ale-giustina/E-ink-buddy/include/bitmaps.h

#ifndef BITMAPS_H
#define BITMAPS_H
#include <map>

// 'Clear_sky', 150x150px
const unsigned char epd_bitmap_Clear_sky [] PROGMEM = {
	0x00, 0x00, 0x00, 0x00, 0x00, 0x00, 0x00, 0x00, 0x00, 0x00, 0x00, 0x00, 0x00, 0x00, 0x00, 0x00, 
	0x00, 0x00, 0x00, 0x00, 0x00, 0x00, 0x00, 0x00, 0x00, 0x00, 0x00, 0x00, 0x00, 0x00, 0x00, 0x00, 
	0x00, 0x00, 0x00, 0x00, 0x00, 0x00, 0x00, 0x00, 0x00, 0x00, 0x00, 0x00, 0x00, 0x00, 0x00, 0x00, 
	0x00, 0x00, 0x00, 0x00, 0x00, 0x00, 0x00, 0x00, 0x00, 0x00, 0x00, 0x00, 0x00, 0x00, 0x00, 0x00, 
	0x00, 0x00, 0x00, 0x00, 0x00, 0x00, 0x00, 0x00, 0x00, 0x00, 0x00, 0x00, 0x00, 0x00, 0x00, 0x00, 
	0x00, 0x00, 0x00, 0x00, 0x00, 0x00, 0x00, 0x00, 0x00, 0x00, 0x00, 0x00, 0x00, 0x00, 0x00, 0x00, 
	0x00, 0x00, 0x00, 0x00, 0x00, 0x00, 0x00, 0x00, 0x00, 0x00, 0x00, 0x00, 0x00, 0x00, 0x00, 0x00, 
	0x00, 0x00, 0x00, 0x00, 0x00, 0x00, 0x00, 0x00, 0x00, 0x00, 0x00, 0x00, 0x00, 0x00, 0x00, 0x00, 
	0x00, 0x00, 0x00, 0x00, 0x00, 0x00, 0x00, 0x00, 0x00, 0x00, 0x00, 0x00, 0x00, 0x00, 0x00, 0x00, 
	0x00, 0x00, 0x00, 0x00, 0x00, 0x00, 0x00, 0x00, 0x00, 0x00, 0x00, 0x00, 0x00, 0x00, 0x00, 0x00, 
	0x00, 0x00, 0x00, 0x00, 0x00, 0x00, 0x00, 0x00, 0x00, 0x00, 0x00, 0x00, 0x00, 0x00, 0x00, 0x00, 
	0x00, 0x00, 0x00, 0x00, 0x00, 0x00, 0x00, 0x00, 0x00, 0x00, 0x00, 0x00, 0x00, 0x00, 0x00, 0x00, 
	0x00, 0x00, 0x00, 0x00, 0x00, 0x00, 0x00, 0x00, 0x00, 0x00, 0x00, 0x00, 0x00, 0x00, 0x00, 0x00, 
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
static const unsigned char* icons_bitmap_allArray[5] = {
	icons_bitmap_bus,
	icons_bitmap_bus,
	icons_bitmap_w_icon,
	icons_bitmap_w_graphs,
	icons_bitmap_w_graphs
};


// Array of all bitmaps for convenience. (Total bytes used to store images in PROGMEM = 51840)

static std::map<int, int> weather_codes_to_btm = {
    {0,  0},   // Clear sky
    {1,  5},   // Mainly clear
    {2,  8},   // Partly cloudy
    {3,  7},   // Overcast
    {45, 2},   // Fog
    {48, 2},   // Depositing rime fog
    {51, 4},   // Drizzle: Light intensity
    {53, 6},   // Drizzle: Moderate intensity
    {55, 1},   // Drizzle: Dense intensity
    {56, 4},   // Freezing Drizzle: Light intensity
    {57, 1},   // Freezing Drizzle: Dense intensity
    {61, 10},  // Rain: Slight intensity
    {63, 9},   // Rain: Moderate intensity
    {65, 11},  // Rain: Heavy intensity
    {66, 10},  // Freezing Rain: Light intensity
    {67, 11},  // Freezing Rain: Heavy intensity
    {71, 13},  // Snow fall: Slight intensity
    {73, 14},  // Snow fall: Moderate intensity
    {75, 17},  // Snow fall: Heavy intensity
    {77, 14},  // Snow grains
    {80, 10},  // Rain showers: Slight
    {81, 11},  // Rain showers: Moderate
    {82, 12},  // Rain showers: Violent
    {85, 13},  // Snow showers: Slight
    {86, 14},  // Snow showers: Heavy
    {95, 3},   // Thunderstorm: Slight or moderate
    {96, 12},  // Thunderstorm with slight hail
    {99, 3}   // Thunderstorm with heavy hail
};



static const int epd_bitmap_allArray_LEN = 18;
static const unsigned char* epd_bitmap_allArray[18] = {
	epd_bitmap_Clear_sky,
	epd_bitmap_Dense_drizzle,
	epd_bitmap_Fog,
	epd_bitmap_Heavy_thunder,
	epd_bitmap_Light_drizzle,
	epd_bitmap_Mainly_clear,
	epd_bitmap_Moderate_drizzle,
	epd_bitmap_Overcast,
	epd_bitmap_Partly_cloudy,
	epd_bitmap_Rain_moderate,
	epd_bitmap_Rain_slight,
	epd_bitmap_Rain_heavy,
	epd_bitmap_Slight_thunder,
	epd_bitmap_Snow_light,
	epd_bitmap_Snow_moderate,
	epd_bitmap_wi_cloud_down,
	epd_bitmap_wi_humidity,
    epd_bitmap_Snow_heavy
};
#endif // _BITMAPS_H_
