ale-giustina/E-ink-buddy/src/helpers.cpp

// Author: Alessandro Giustina
// Description: Utility helper functions and debugging tools

#include <helpers.h>

// Returns formatted part of the local time
String time_helper(char c) {
    struct tm timeinfo;
    if (getLocalTime(&timeinfo)) {
        switch (c) {
            case 'H': return timeinfo.tm_hour < 10 ? "0" + String(timeinfo.tm_hour) : String(timeinfo.tm_hour);
            case 'M': return timeinfo.tm_min < 10 ? "0" + String(timeinfo.tm_min) : String(timeinfo.tm_min);
            case 'S': return timeinfo.tm_sec < 10 ? "0" + String(timeinfo.tm_sec) : String(timeinfo.tm_sec);
            case 'd': return timeinfo.tm_mday < 10 ? "0" + String(timeinfo.tm_mday) : String(timeinfo.tm_mday);
            case 'm': return (timeinfo.tm_mon + 1) < 10 ? "0" + String(timeinfo.tm_mon + 1) : String(timeinfo.tm_mon + 1);
            case 'Y': return String(timeinfo.tm_year + 1900);
            default: return "";
        }
    }
    return "";
}

// Prints timestamp in "YYYY-MM-DD HH:MM:SS - " format
void print_timestamp() {
    String timestamp = String(time_helper('Y')) + "-" + String(time_helper('m')) + "-" + String(time_helper('d')) + " " +
                       String(time_helper('H')) + ":" + String(time_helper('M')) + ":" + String(time_helper('S')) + " - ";
    Serial.print(timestamp);
}

bool enable_debug = false;

void debug_println(const String& message, bool override_debug) {
    if (enable_debug || override_debug) {
        Serial.println(message);
    }
}
void debug_print(const String& message, bool override_debug) {
    if (enable_debug || override_debug) {
        Serial.print(message);
    }
}

void debug_print_routes(const RouteInfo* routes, int count, bool override_debug) {
    if (enable_debug || override_debug) {
        for(int i = 0; i < count; i++) {
            print_timestamp();
            Serial.print("Route: ");
            Serial.print(routes[i].shortName);
            Serial.print(", ");
            Serial.print(routes[i].longName);
            Serial.print(", Delay: ");
            Serial.print(routes[i].delay);
            Serial.print(" min, ETA: ");
            Serial.println(routes[i].eta);
        }
    }
}

void debug_print_weather_5d(const Weather_5D& weather, bool override_debug) {
    if (enable_debug || override_debug) {
        print_timestamp();
        Serial.println("5-Day Weather Forecast:");
        for (int i = 0; i < 5; i++) {
            Serial.print("Day ");
            Serial.print(i + 1);
            Serial.print(": Code=");
            Serial.print(weather.codes[i]);
            Serial.print(", Temp Min=");
            Serial.print(weather.temp_min[i]);
            Serial.print(", Temp Max=");
            Serial.print(weather.temp_max[i]);
            Serial.print(", Precipitation Probability=");
            Serial.println(weather.precipitation[i]);
        }
    }
}

void debug_print_weather_24h(const Weather_24H& weather, bool override_debug) {
    if (enable_debug || override_debug) {
        print_timestamp();
        Serial.println("24-Hour Weather Forecast:");
        Serial.print("Code=");
        Serial.print(weather.code);
        Serial.print(", Temp Min=");
        Serial.print(weather.temp_min);
        Serial.print(", Temp Max=");
        Serial.println(weather.temp_max);
        Serial.println("Hourly Precipitation Probability:");
        for (int i = 0; i < 24; i++) {
            Serial.print(weather.precipitation[i]);
            Serial.print("% - ");
        }
        Serial.println();
        Serial.println("Hourly Temperature:");
        for (int i = 0; i < 24; i++) {
            Serial.print(weather.temperature[i]);
            Serial.print("C° - ");
        }
        Serial.println();
    }
}

void debug_print_weather_now(const Weather_now& weather, bool override_debug) {
    if (enable_debug || override_debug) {
        print_timestamp();
        Serial.println("Current Weather:");
        Serial.print("Code=");
        Serial.print(weather.code);
        Serial.print(", Temp=");
        Serial.print(weather.temp);
        Serial.print(", Windspeed=");
        Serial.print(weather.windspeed);
        Serial.print(", Precipitation Probability=");
        Serial.print(weather.precipitation_probability);
        Serial.print(", Humidity=");
        Serial.println(weather.humidity);
    }
}

bool is_connected() {

    // I found WL_CONNECTED to not be reliable enough on its own so this
    // makes a lightweight HTTP request to confirm connectivity
    // This is run every minute

    if (WiFi.status() != WL_CONNECTED) return false;

    HTTPClient http;
    http.begin("http://clients3.google.com/generate_204"); // lightweight test
    int httpCode = http.GET();
    http.end();

    return (httpCode == 204);
}

bool is_DST(int year, int month, int day, int hour) {

    // The oraArrivoAFermataSelezionata provides the time in a wierd way
    // only time will tell if this is the correct solution

    // DST: from last Sunday in March 2:00 → last Sunday in October 3:00
    if (month < 3 || month > 10) return false;
    if (month > 3 && month < 10) return true;

    int lastSunday;
    if (month == 3) {
    // Find last Sunday in March
    lastSunday = 31 - ((5 * year / 4 + 4) % 7);
    return (day > lastSunday || (day == lastSunday && hour >= 2));
    } else if (month == 10) {
    // Find last Sunday in October
    lastSunday = 31 - ((5 * year / 4 + 1) % 7);
    return !(day > lastSunday || (day == lastSunday && hour >= 3));
    }
    return false;
}

int calc_delta_time(const String& eta_str) {

    struct tm now;
    getLocalTime(&now);

    int now_total_minutes = now.tm_hour * 60 + now.tm_min;

    int eta_hour = 0;
    int eta_minute = 0;

    sscanf(eta_str.c_str(), "%d:%d", &eta_hour, &eta_minute);

    int eta_total_minutes = eta_hour * 60 + eta_minute;

    int delta_minutes = eta_total_minutes - now_total_minutes;
    if (delta_minutes < -600) {
        delta_minutes += 24 * 60; // Adjust for next day only if difference is more than 10 hours negative
    }

    return delta_minutes;
}
