ale-giustina/E-ink-buddy/src/weather.cpp

// Author: Alessandro Giustina
// Description: Weather data handling implementation file

#include <weather.h>

// Map of weather codes to descriptions
std::map<int, String> weather_codes = {
    {0,  "Clear sky"},
    {1,  "Mainly clear"},
    {2,  "Partly cloudy"},
    {3,  "Overcast"},
    {45, "Fog"},
    {48, "Depositing rime fog"},
    {51, "Drizzle: Light intensity"},
    {53, "Drizzle: Moderate intensity"},
    {55, "Drizzle: Dense intensity"},
    {56, "Freezing Drizzle: Light intensity"},
    {57, "Freezing Drizzle: Dense intensity"},
    {61, "Rain: Slight intensity"},
    {63, "Rain: Moderate intensity"},
    {65, "Rain: Heavy intensity"},
    {66, "Freezing Rain: Light intensity"},
    {67, "Freezing Rain: Heavy intensity"},
    {71, "Snow fall: Slight intensity"},
    {73, "Snow fall: Moderate intensity"},
    {75, "Snow fall: Heavy intensity"},
    {77, "Snow grains"},
    {80, "Rain showers: Slight"},
    {81, "Rain showers: Moderate"},
    {82, "Rain showers: Violent"},
    {85, "Snow showers: Slight"},
    {86, "Snow showers: Heavy"},
    {95, "Thunderstorm: Slight or moderate"},
    {96, "Thunderstorm with slight hail"},
    {99, "Thunderstorm with heavy hail"}
};

String latitude = "46.0679";
String longitude = "11.1211";

void get_weather_5d(Weather_5D &w_ob, bool force_update){

    struct tm now;

    getLocalTime(&now);

    // Check if update is needed
    if(w_ob.last_update.tm_sec==-1 || w_ob.last_update.tm_min<now.tm_min-WEATHER_EXP_5D || w_ob.last_update.tm_hour!=now.tm_hour || force_update){

        debug_println("Updating...");

        HTTPClient weatherClient;

        String url = "https://api.open-meteo.com/v1/forecast?latitude=" + latitude + "&longitude=" + longitude + "&daily=weather_code,temperature_2m_max,temperature_2m_min,precipitation_probability_max&hourly=temperature_2m,precipitation_probability&models=best_match&timezone=Europe%2FBerlin&forecast_days=14";

        weatherClient.begin(url);
        int httpCode = weatherClient.GET();
        debug_println(String("Code: ")+String(httpCode));
        if (httpCode == 200) {
            
            String payload = weatherClient.getString();
            JsonDocument doc;
            
            if (!deserializeJson(doc, payload)) {
            
                JsonObject root = doc.as<JsonObject>();

                JsonObject daily = root["daily"];
                int inx = 0;

                getLocalTime(&w_ob.last_update);

                for (JsonVariant v : daily["weather_code"].as<JsonArray>()) {
                    w_ob.codes[inx++] = v.as<short>();
                    if(inx==14)break;
                }
                inx = 0;
                for (JsonVariant v : daily["temperature_2m_max"].as<JsonArray>()) {
                    w_ob.temp_max[inx++] = v.as<float>();
                    if(inx==14)break;
                }
                inx = 0;
                for (JsonVariant v : daily["temperature_2m_min"].as<JsonArray>()) {
                    w_ob.temp_min[inx++] = v.as<float>();
                    if(inx==14)break;
                }
                inx = 0;
                for (JsonVariant v : daily["precipitation_probability_max"].as<JsonArray>()) {
                    w_ob.precipitation[inx++] = v.as<short>();
                    if(inx==14)break;
                }
                inx = 0;
                JsonObject hourly = root["hourly"];
                for (JsonVariant v : hourly["temperature_2m"].as<JsonArray>()) {
                    w_ob.temperature[inx++] = v.as<float>();
                    if(inx==336)break;
                }
                inx = 0;
                for (JsonVariant v : hourly["precipitation_probability"].as<JsonArray>()) {
                    w_ob.precipitation_probability[inx++] = v.as<short>();
                    if(inx==336)break;
                }

            } else {
            Serial.println("Failed to parse 5d weather JSON");
            debug_println(payload);
            }
        } else {
            Serial.printf("Failed to fetch weather, HTTP code: %d\n", httpCode);
        }
        weatherClient.end();
    }
    else{
        debug_println(String("Using cache"));
    }

}

void get_weather_24h(Weather_24H &w_ob, bool force_update){

    struct tm now;

    getLocalTime(&now);

    // Check if update is needed
    if(w_ob.last_update.tm_sec==-1 || w_ob.last_update.tm_min<now.tm_min-WEATHER_EXP_24H || w_ob.last_update.tm_hour!=now.tm_hour || force_update){

        debug_println("Updating...");

        HTTPClient weatherClient;

        String url = "https://api.open-meteo.com/v1/forecast?latitude=" + latitude + "&longitude=" + longitude + "&daily=temperature_2m_max,temperature_2m_min,weather_code&hourly=temperature_2m,precipitation_probability,relative_humidity_2m,cloud_cover&models=best_match&timezone=Europe%2FBerlin&forecast_days=7";

        weatherClient.begin(url);
        int httpCode = weatherClient.GET();
        debug_println(String("Code: ")+String(httpCode));
        if (httpCode == 200) {
            
            String payload = weatherClient.getString();
            JsonDocument doc;
            
            if (!deserializeJson(doc, payload)) {
            
                JsonObject root = doc.as<JsonObject>();

                JsonObject daily = root["daily"];

                getLocalTime(&w_ob.last_update);

                w_ob.code = daily["weather_code"][0].as<short>();
                w_ob.temp_max = daily["temperature_2m_max"][0].as<float>();
                w_ob.temp_min = daily["temperature_2m_min"][0].as<float>();
                int inx = 0;
                JsonObject hourly = root["hourly"];
                for (JsonVariant v : hourly["precipitation_probability"].as<JsonArray>()) {
                    w_ob.precipitation[inx++] = v.as<short>();
                    if(inx==168)break;
                }
                inx = 0;
                for (JsonVariant v : hourly["temperature_2m"].as<JsonArray>()) {
                    w_ob.temperature[inx++] = v.as<float>();
                    if(inx==168)break;
                }
                inx = 0;
                for (JsonVariant v : hourly["relative_humidity_2m"].as<JsonArray>()) {
                    w_ob.humidity[inx++] = v.as<short>();
                    if(inx==168)break;
                }
                inx = 0;
                for (JsonVariant v : hourly["cloud_cover"].as<JsonArray>()) {
                    w_ob.cloudcover[inx++] = v.as<float>();
                    if(inx==168)break;
                }

            } else {
            Serial.println("Failed to parse 24h weather JSON");
            debug_println(payload);
            }
        } else {
            Serial.printf("Failed to fetch weather, HTTP code: %d\n", httpCode);
        }
        weatherClient.end();
    }
    else{
        debug_println(String("Using cache"));
    }

}

void get_current_weather(Weather_now &w_ob, bool force_update){

    struct tm now;

    getLocalTime(&now);

    // Check if update is needed
    if(w_ob.last_update.tm_sec==-1 || w_ob.last_update.tm_min<now.tm_min-WEATHER_EXP_NOW || w_ob.last_update.tm_hour!=now.tm_hour || force_update){

        debug_println("Updating...");

        HTTPClient weatherClient;

        String url = "https://api.open-meteo.com/v1/forecast?latitude=" + latitude + "&longitude=" + longitude + "&models=best_match&current=temperature_2m,relative_humidity_2m,precipitation,weather_code,wind_speed_10m&timezone=Europe%2FBerlin&forecast_days=1";

        weatherClient.begin(url);
        int httpCode = weatherClient.GET();
        debug_println(String("Code: ")+String(httpCode));
        if (httpCode == 200) {
            
            String payload = weatherClient.getString();
            JsonDocument doc;
            
            if (!deserializeJson(doc, payload)) {
            
                JsonObject root = doc.as<JsonObject>();

                JsonObject current = root["current"];

                getLocalTime(&w_ob.last_update);

                w_ob.code = current["weather_code"].as<short>();
                w_ob.temp = current["temperature_2m"].as<float>();
                w_ob.humidity = current["relative_humidity_2m"].as<float>();
                w_ob.precipitation_probability = current["precipitation"].as<short>();
                w_ob.windspeed = current["wind_speed_10m"].as<float>();

            } else {
            Serial.println("Failed to parse current weather JSON");
            debug_println(payload);
            }
        } else {
            Serial.printf("Failed to fetch weather, HTTP code: %d\n", httpCode);
        }
        weatherClient.end();
    }
    else{
        debug_println(String("Using cache"));
    }

}
