ale-giustina/E-ink-buddy/include/secrets_example.h

#pragma once
#define WIFI_SSID "Your_SSID_Here"
#define WIFI_PASSWORD "Your_Password_Here"
#define API_KEY "Your_API_Key_Here"
#define TT_BASE_URL "https://app-tpl.tndigit.it/gtlservice"
#define TT_USER "Your_Username_Here"
#define TT_PASS "Your_Password_Here"
